HieuTran2019/CDS-UTE---Documentation-Project/docs/source/_static/ute_ai_lab.jpg

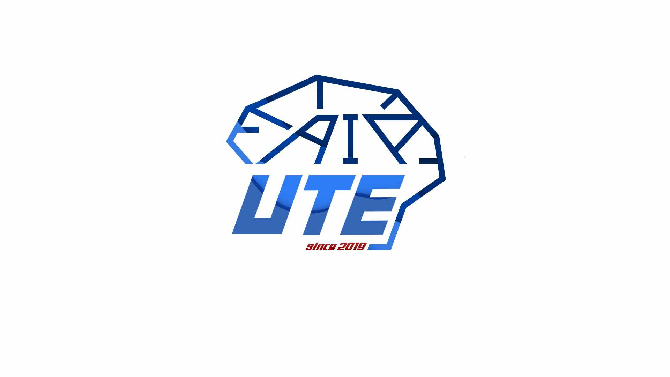
docs/source/_static/ute_ai_lab.jpg
