HieuTran2019/CDS-UTE---Documentation-Project/docs/source/challenges/maps/Traffic_signs/images/bien_cam_di_nguoc_chieu.jpg

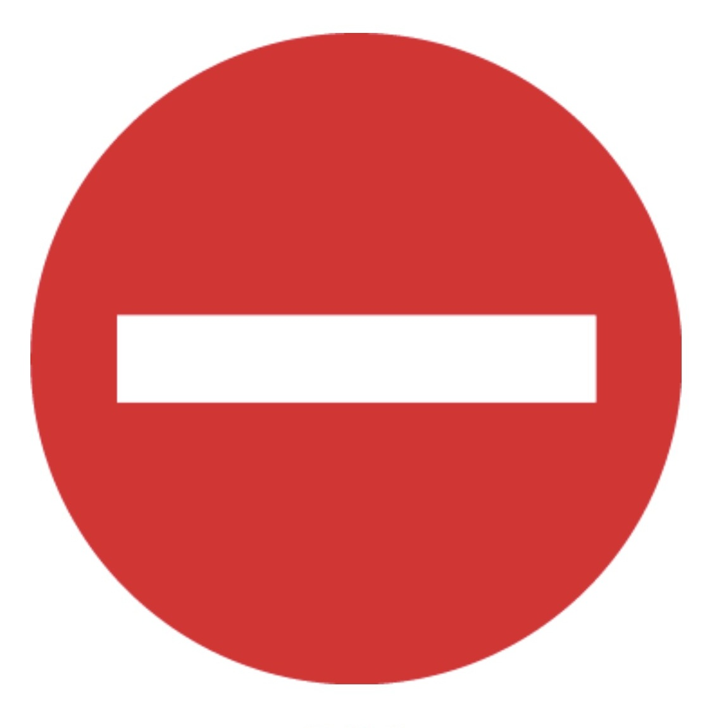
docs/source/challenges/maps/Traffic_signs/images/bien_cam_di_nguoc_chieu.jpg
