HieuTran2019/CDS-UTE---Documentation-Project/docs/source/challenges/maps/Traffic_signs/images/bien_cam_di_thang.jpg

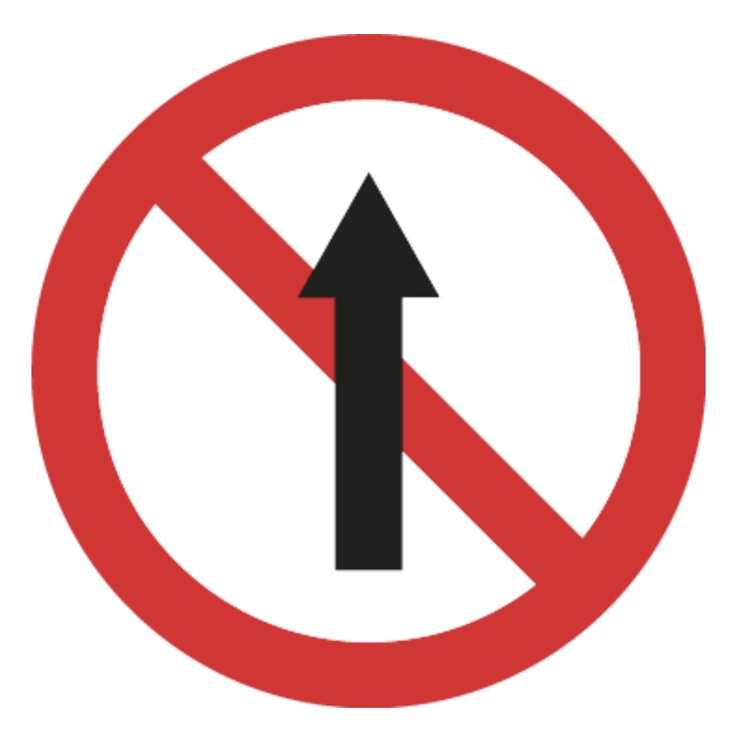
docs/source/challenges/maps/Traffic_signs/images/bien_cam_di_thang.jpg
