HieuTran2019/CDS-UTE---Documentation-Project/docs/source/challenges/maps/Traffic_signs/images/bien_cam_re_trai.jpg

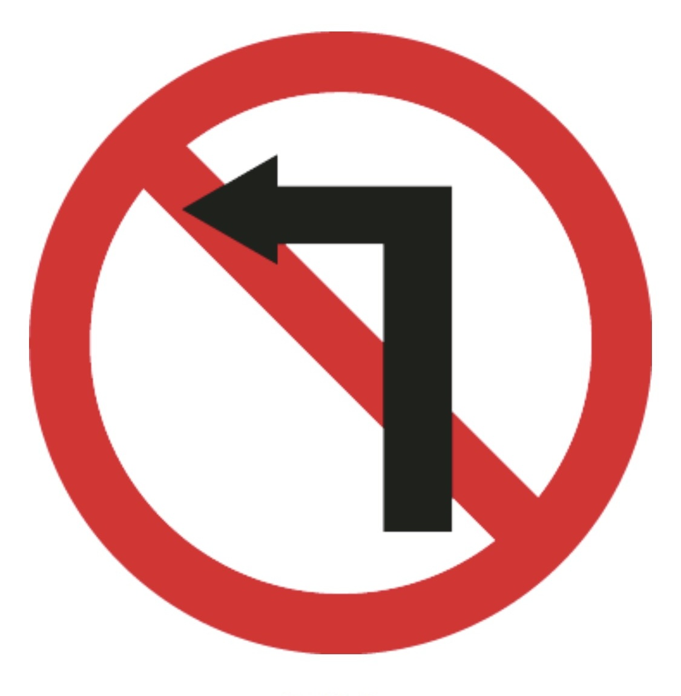
docs/source/challenges/maps/Traffic_signs/images/bien_cam_re_trai.jpg
