HieuTran2019/CDS-UTE---Documentation-Project/docs/source/challenges/maps/Traffic_signs/images/bien_duong_uu_tien.jpg

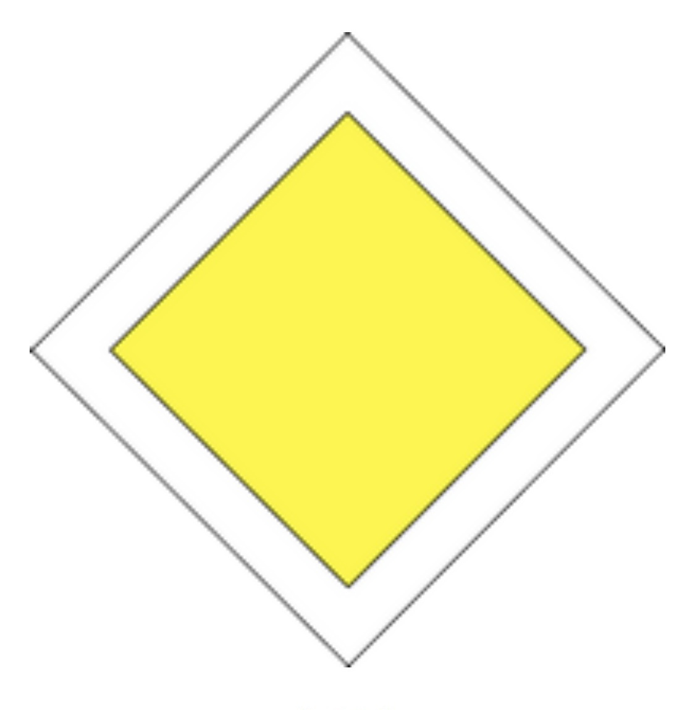
docs/source/challenges/maps/Traffic_signs/images/bien_duong_uu_tien.jpg
